pozsarzs/ctt-hw/photos/ctt-ps1.jpg

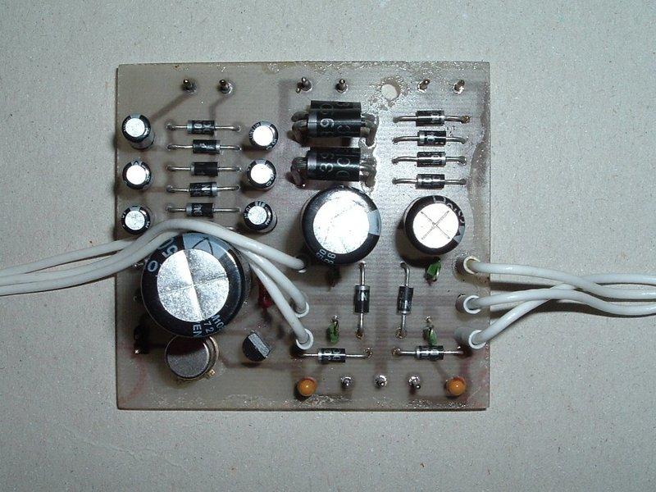
photos/ctt-ps1.jpg
