pozsarzs/ctt-hw/photos/ctt-ps3.jpg

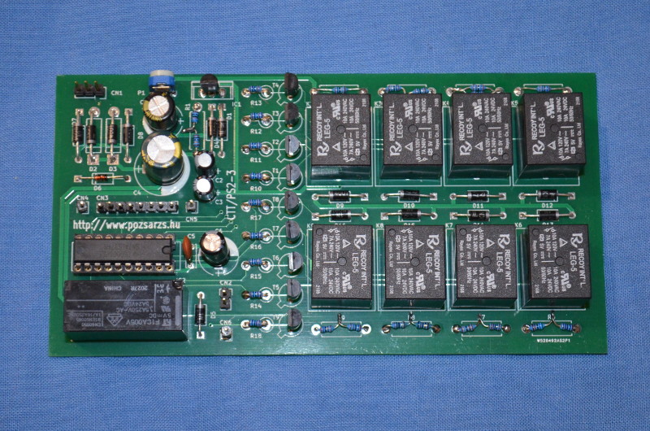
photos/ctt-ps3.jpg
