pozsarzs/ctt-hw/photos/ctt-sw1.jpg

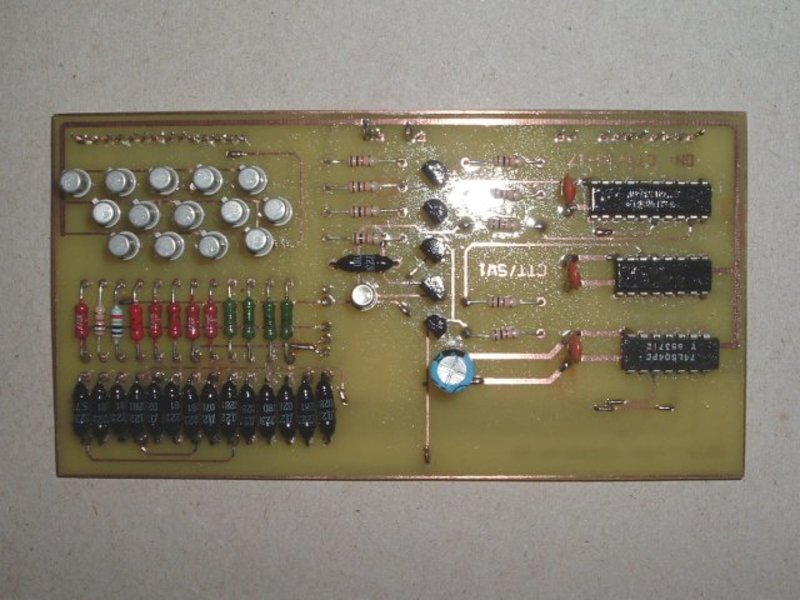
photos/ctt-sw1.jpg
