pozsarzs/ctt-hw/photos/ctt-sw2.jpg

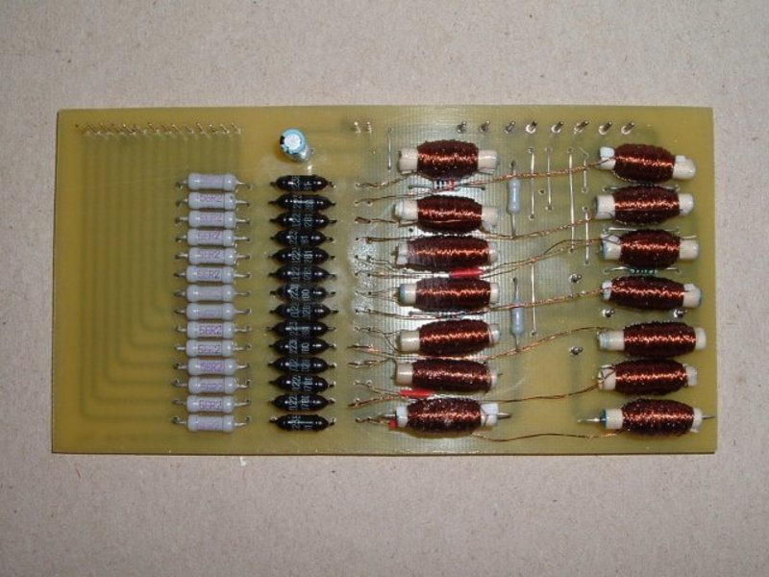
photos/ctt-sw2.jpg
