pozsarzs/ctt-hw/documents/sch_ctt-sw1.pdf

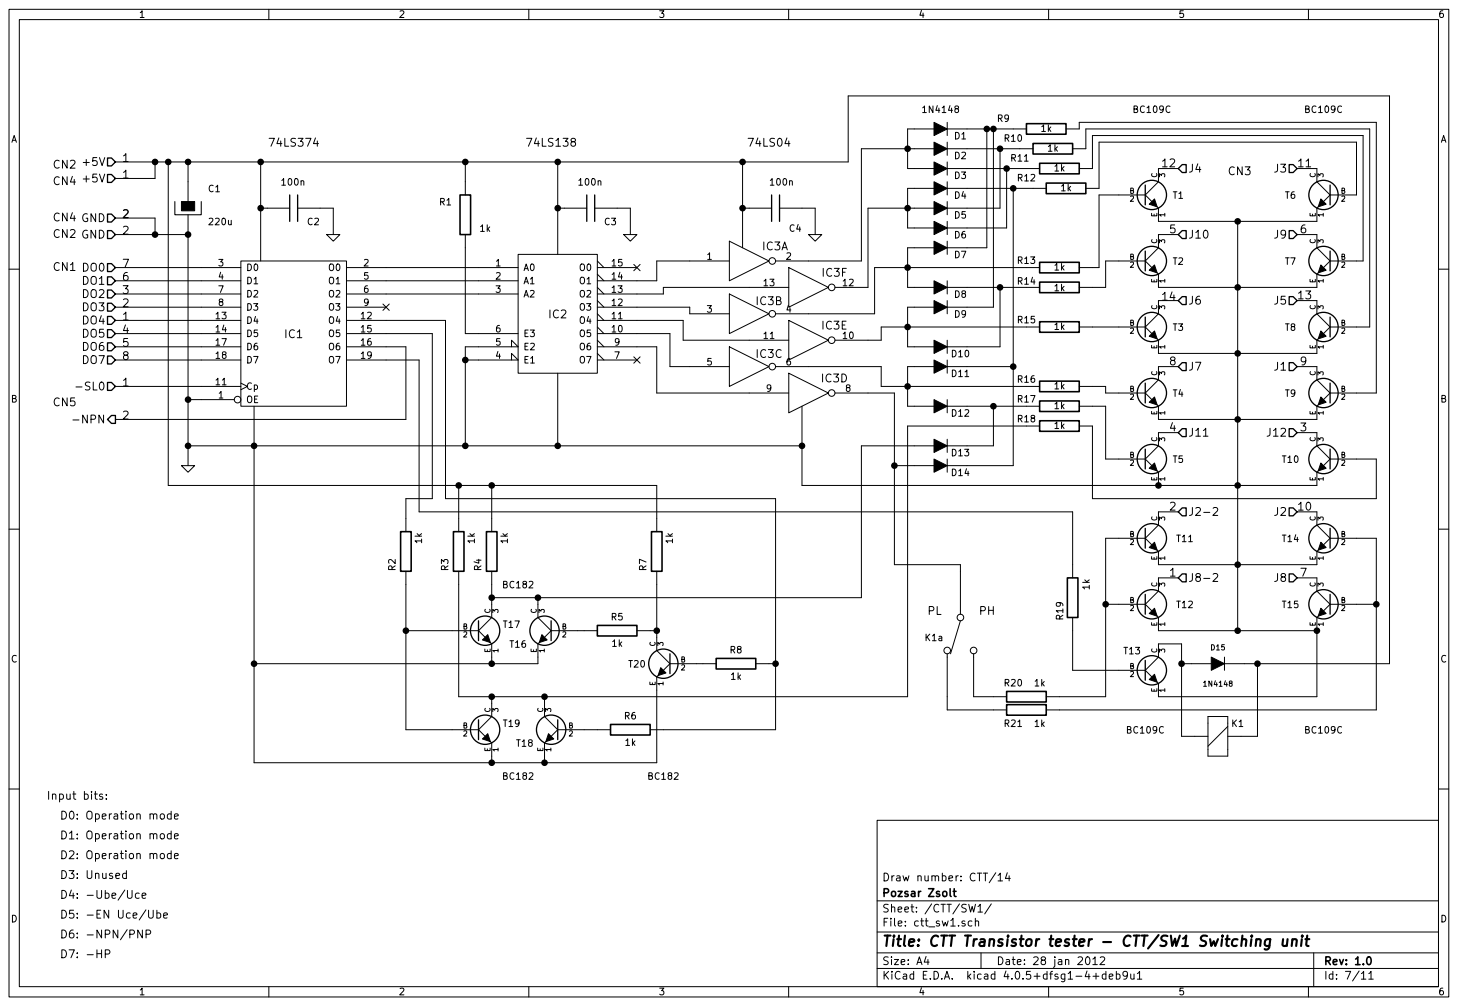
[picture p22: page 1]

D1: Operation mode
D2: Operation mode D3: Unused D4: -Ube/Uce

Id: 7/11 Title: CTT Transistor tester - CTT/SW1 Switching unit
