pozsarzs/ctt-hw/documents/sch_ctt-sw2.pdf

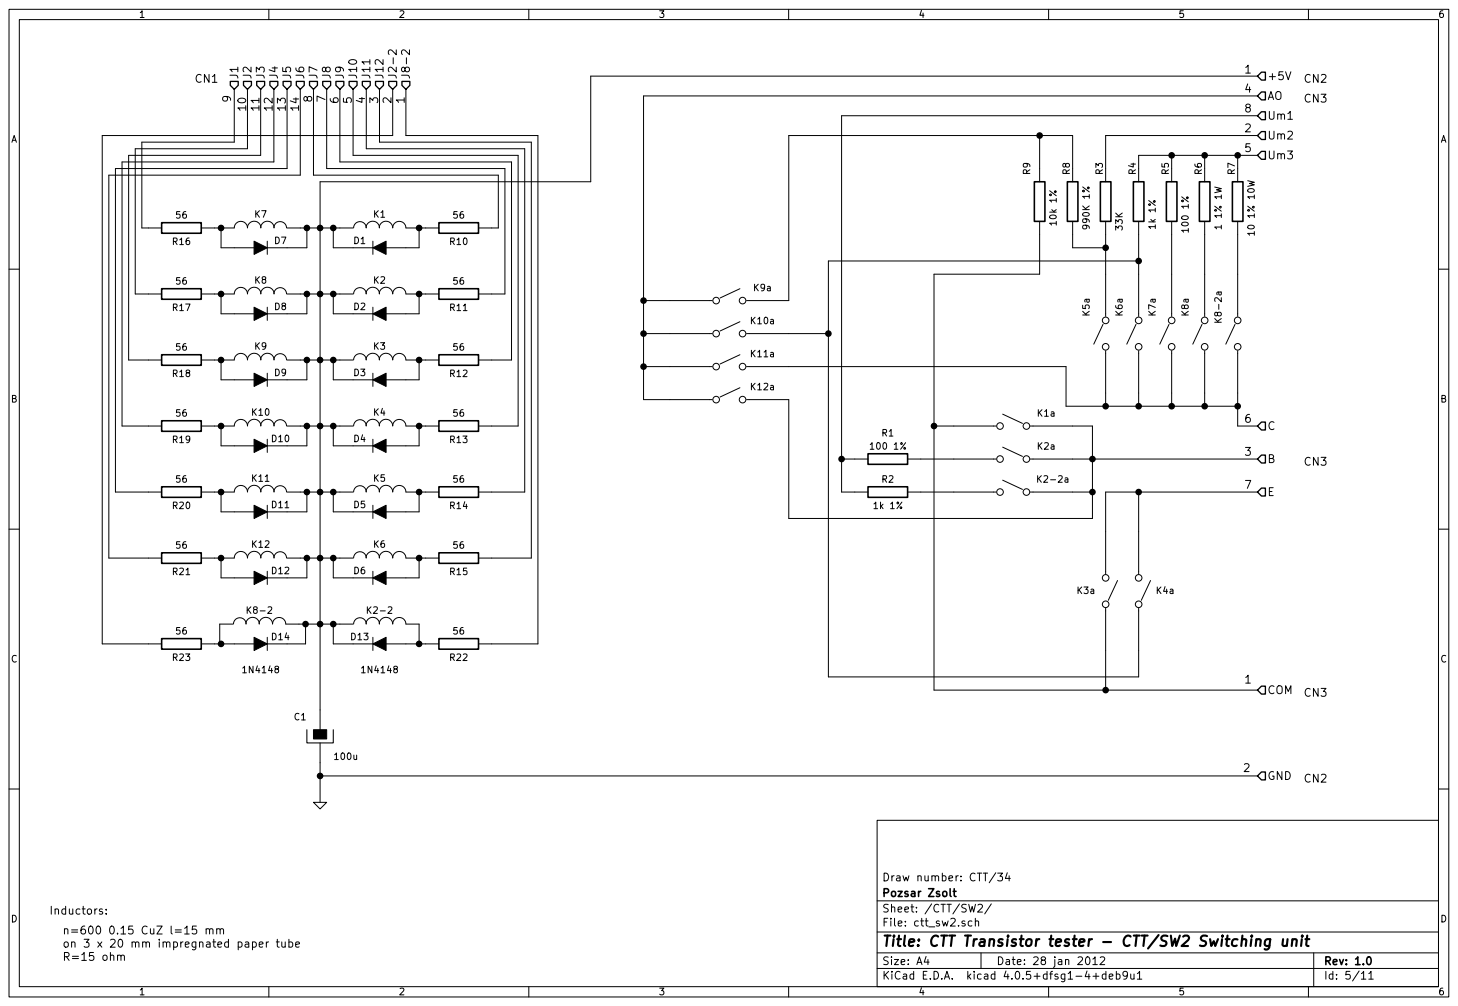
[picture p23: page 1]

File: ctt_sw2.sch Sheet: /CTT/SW2/ Pozsar Zsolt Draw number: CTT/34 on 3 x 20 mm impregnated paper tube R=15 ohm

Id: 5/11 Title: CTT Transistor tester - CTT/SW2 Switching unit
