pozsarzs/ctt-hw/documents/pcb_ctt-sw2-silk.pdf

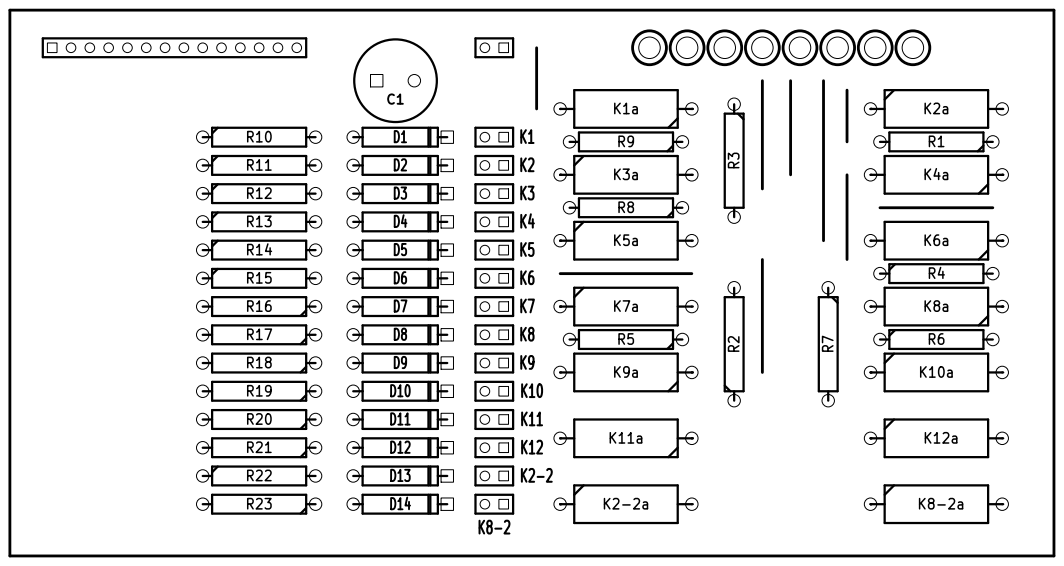
[picture p24: page 1]

File: ctt_sw2.kicad_pcb Sheet: Pozsar Zsolt Draw number: CTT/32-33

Id: 1/1 Title: CTT Transistor tester - CTT/SW2 Switching unit
