pozsarzs/ctt-hw/documents/pcb_ctt-ad-comp.pdf

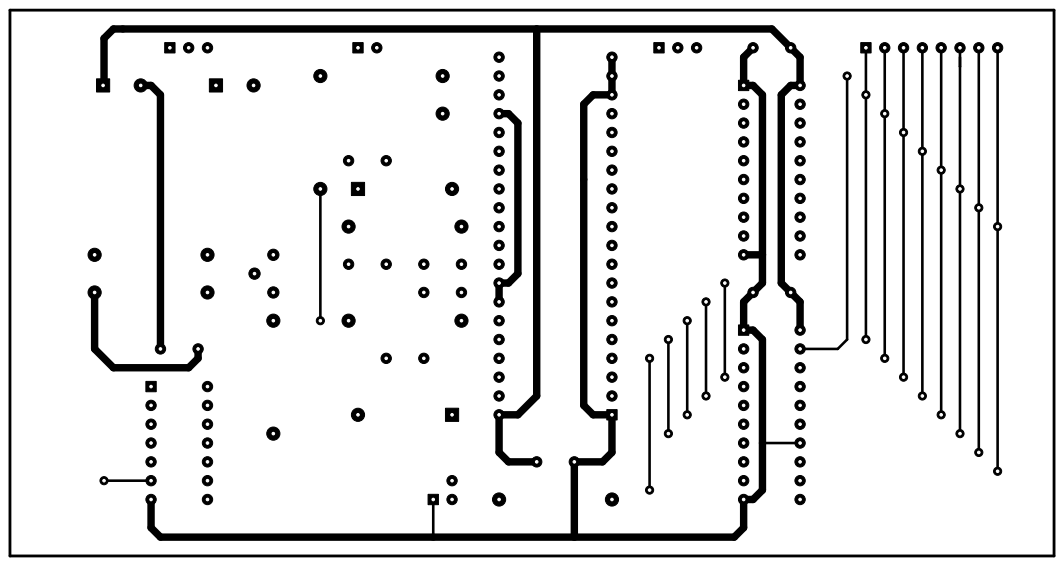
[picture p25: page 1]

File: ctt_ad.kicad_pcb Sheet: Pozsar Zsolt Draw number: CTT/11-13

Id: 1/1 Title: CTT Transistor tester - CTT/AD A/D converter unit
