pozsarzs/ctt-hw/documents/pcb_ctt-dp-comp.pdf

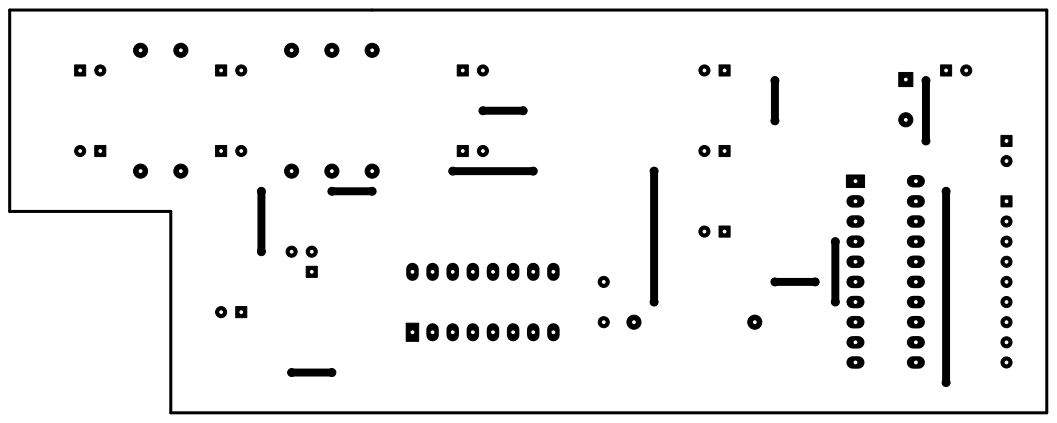
[picture p26: page 1]

File: ctt_dp.kicad_pcb Sheet: Pozsar Zsolt Draw number: CTT/8-9

Id: 1/1 Title: CTT Transistor tester - CTT/DP Display unit
