pozsarzs/ctt-hw/documents/pcb_ctt-if-comp.pdf

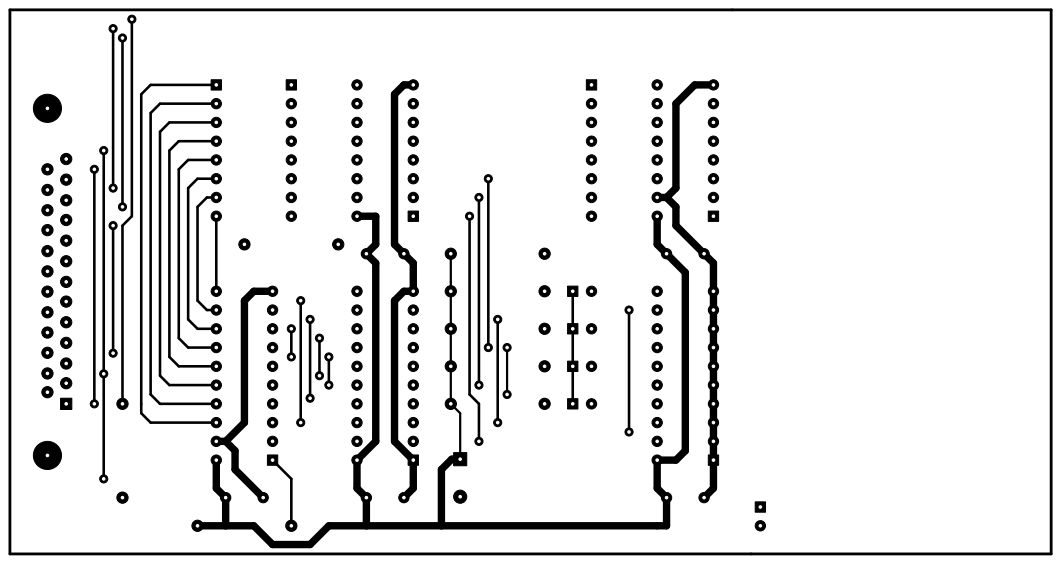
[picture p27: page 1]

File: ctt_if.kicad_pcb Sheet: Pozsar Zsolt Draw number: CTT/4-6

Id: 1/1 Title: CTT Transistor tester - CTT/IF Interface unit
