pozsarzs/ctt-hw/documents/pcb_ctt-ps1-silk.pdf

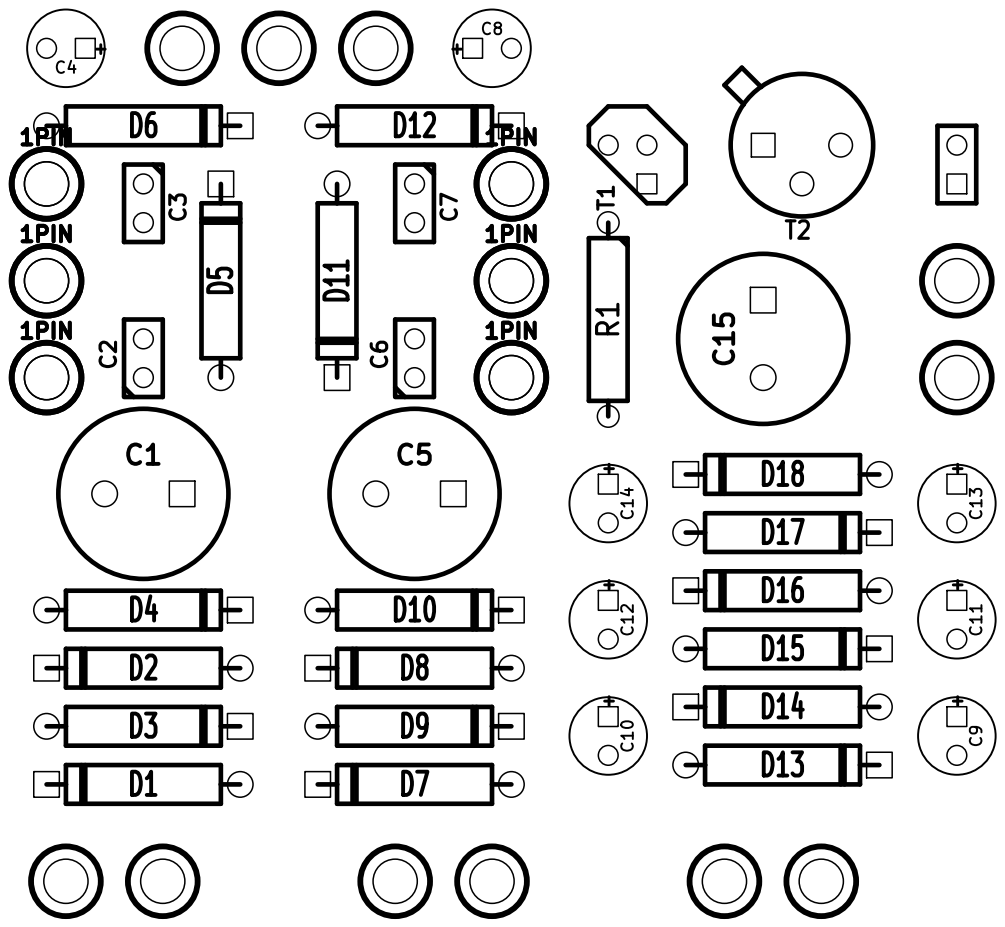
[picture p28: page 1]

File: ctt_ps1.kicad_pcb Sheet: Pozsar Zsolt Draw number: CTT/22-23

Id: 1/1 Title: CTT Transistor tester - CTT/PS1 Power supply unit
