pozsarzs/ctt-hw/documents/pcb_ctt-sc-comp.pdf

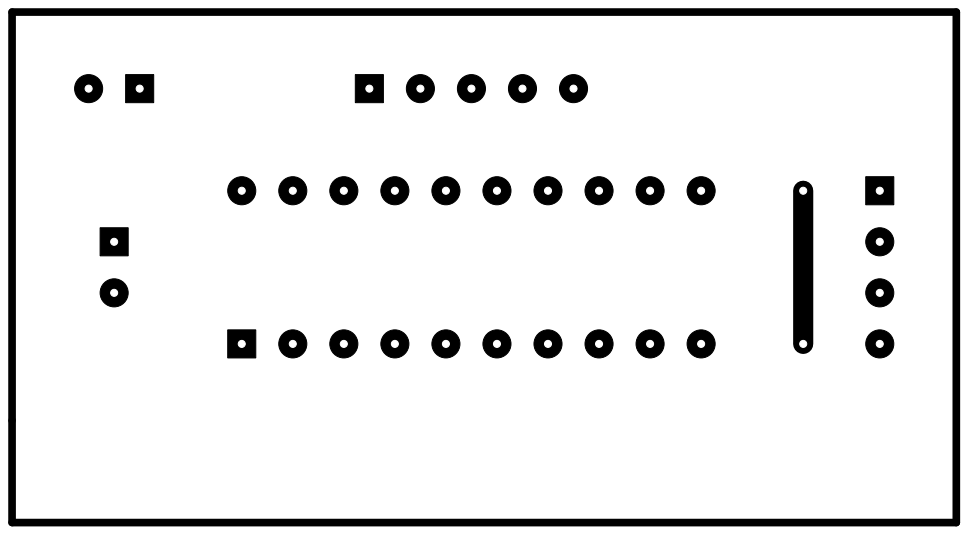
[picture p30: page 1]

File: ctt_sc.kicad_pcb Sheet: Pozsar Zsolt Draw number: CTT/41-42

Id: 1/1 Title: CTT Transistor tester - CTT/SC Status collector unit
