pozsarzs/ctt-hw/documents/pcb_ctt-sc-sold.pdf

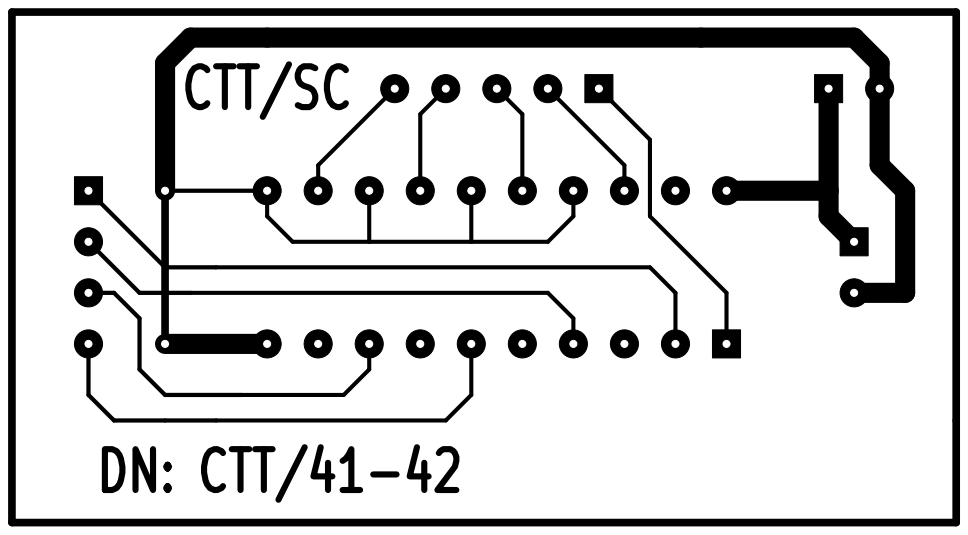
[picture p31: page 1]

File: ctt_sc.kicad_pcb Sheet: Pozsar Zsolt Draw number: CTT/41-42 DN: CTT/41-42

Id: 1/1 Title: CTT Transistor tester - CTT/SC Status collector unit
