pozsarzs/ctt-hw/documents/pcb_ctt-sw1-comp.pdf

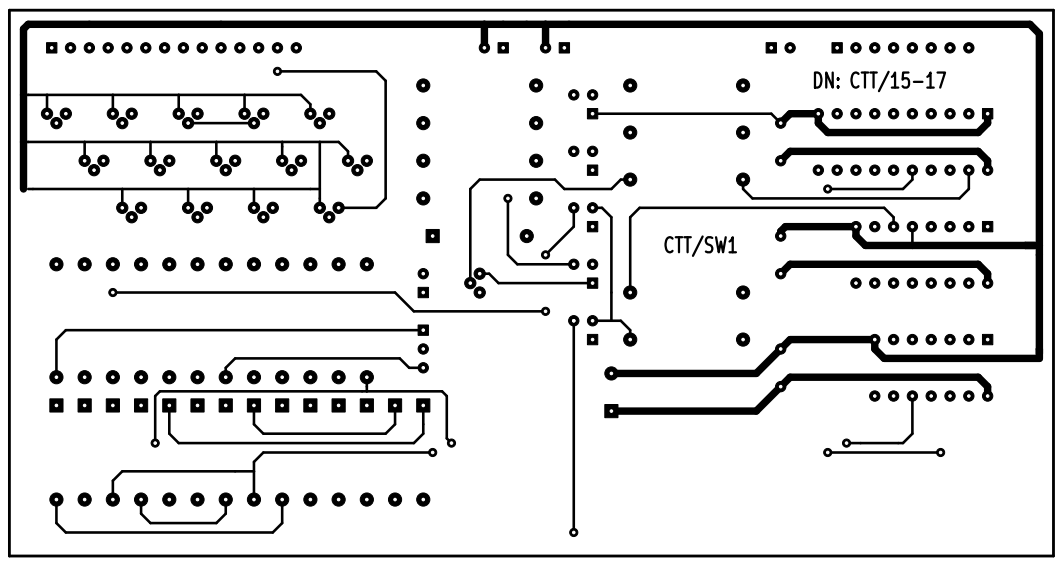
[picture p32: page 1]

File: ctt_sw1.kicad_pcb Sheet: Pozsar Zsolt Draw number: CTT/15-17 CTT/SW1

Id: 1/1 Title: CTT Transistor tester - CTT/SW1 Switching unit
