pozsarzs/ctt-hw/documents/pcb_ctt-sw1-silk.pdf

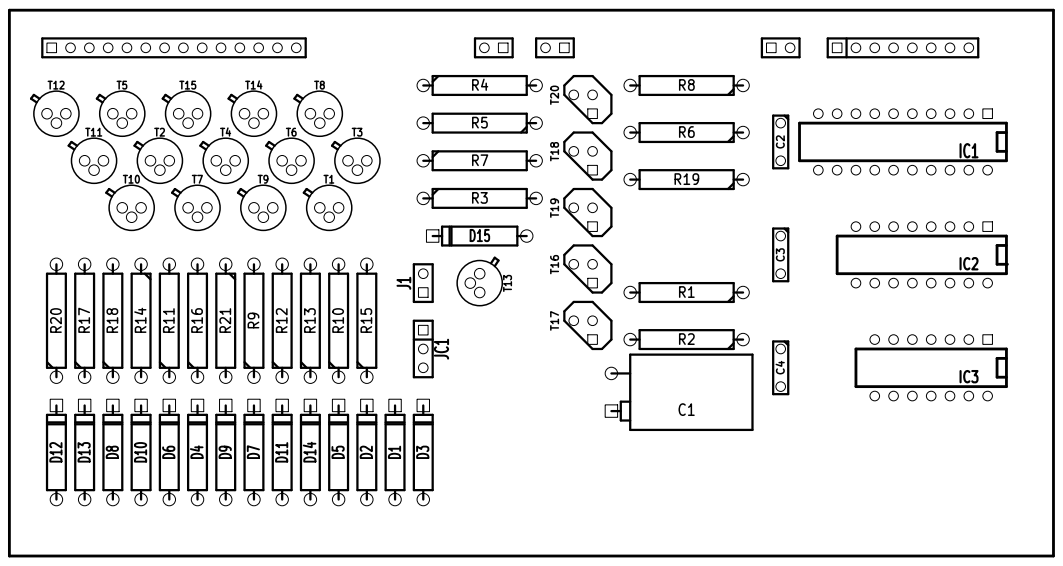
[picture p33: page 1]

File: ctt_sw1.kicad_pcb Sheet: Pozsar Zsolt Draw number: CTT/15-17 C2 C3 C4

Id: 1/1 Title: CTT Transistor tester - CTT/SW1 Switching unit
