pozsarzs/ctt-hw/documents/pcb_ctt-sw1-sold.pdf

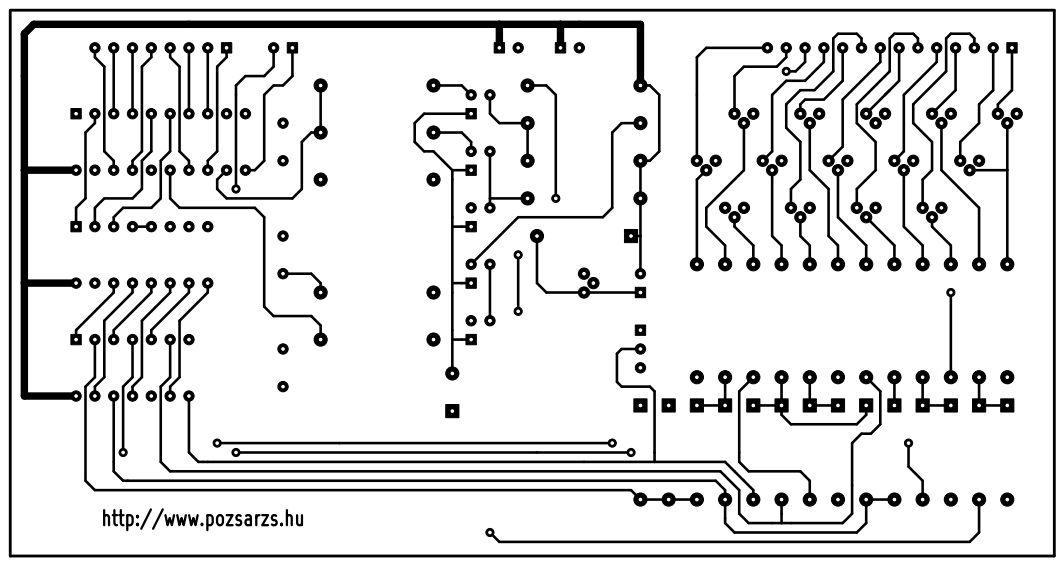
[picture p34: page 1]

File: ctt_sw1.kicad_pcb Sheet: Pozsar Zsolt Draw number: CTT/15-17 http://www.pozsarzs.hu

Id: 1/1 Title: CTT Transistor tester - CTT/SW1 Switching unit
