pozsarzs/ctt-hw/documents/pcb_ctt-sw2-sold.pdf

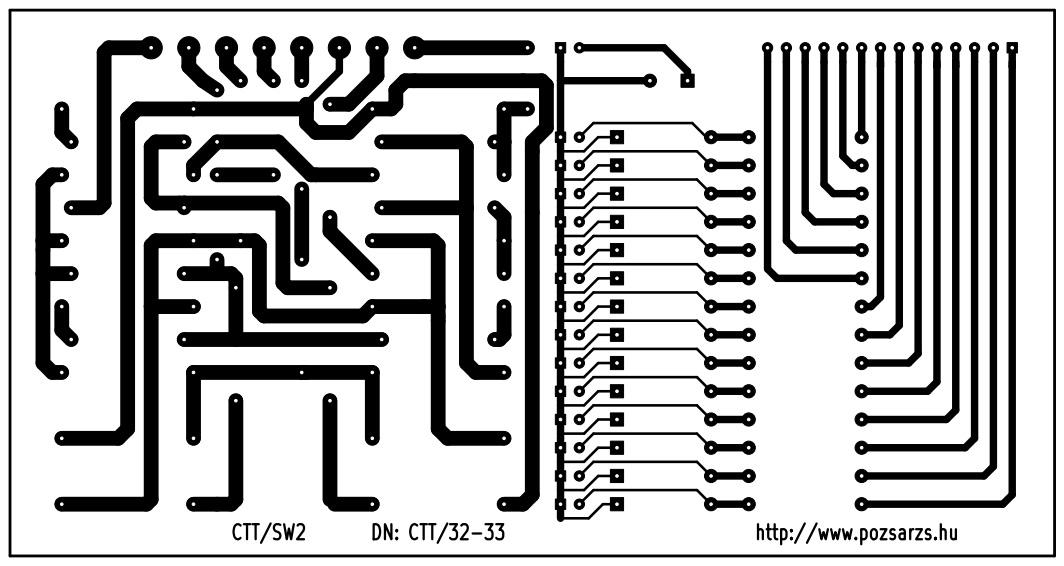
[picture p35: page 1]

Id: 1/1 Title: CTT Transistor tester - CTT/SW2 Switching unit
