pozsarzs/ctt-hw/documents/sch_ctt-ps1.pdf

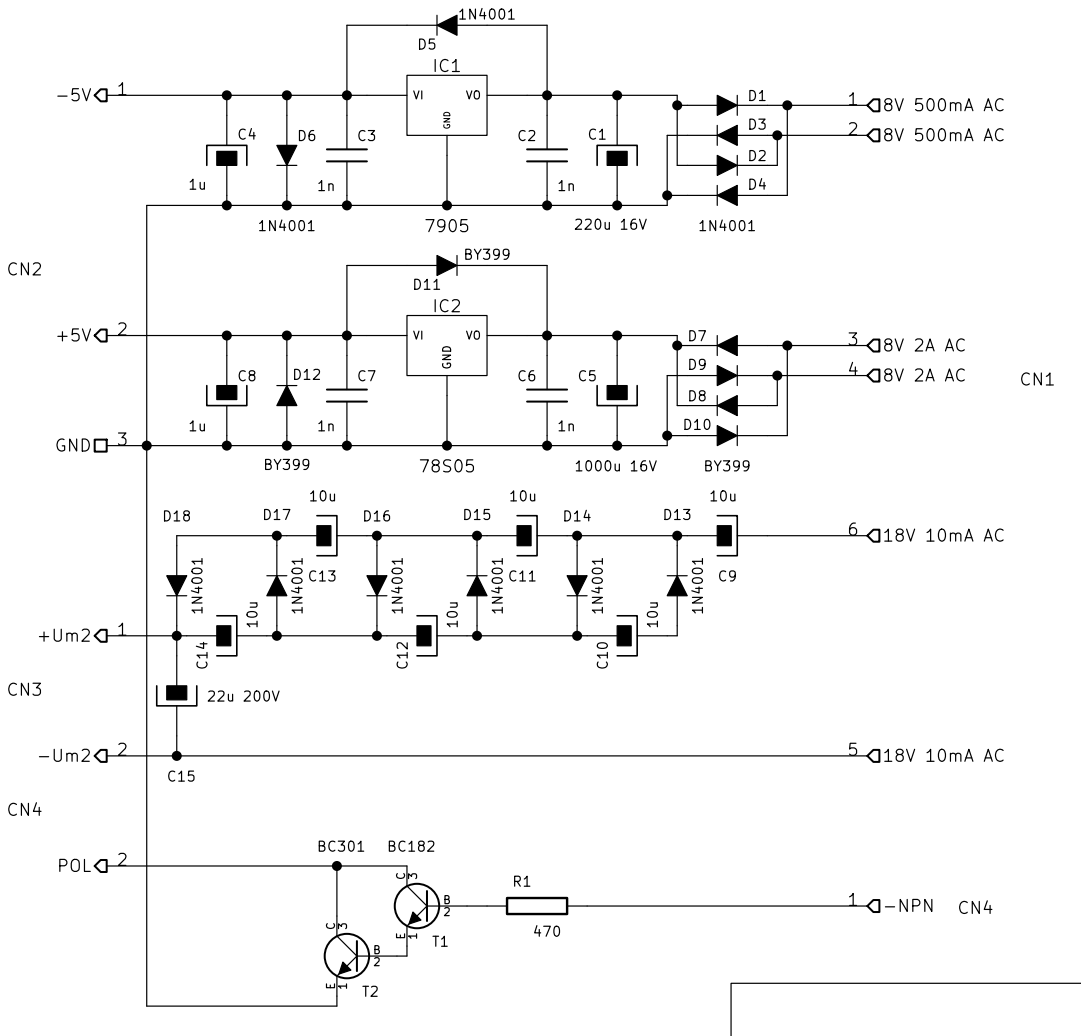
[picture p36: page 1]

File: ctt_ps1.sch Sheet: /CTT/PS1/ Pozsar Zsolt Draw number: CTT/21 6

Id: 11/11 Title: CTT Transistor tester - CTT/PS1 power supply unit
