pozsarzs/ctt-hw/documents/sch_ctt-ad.pdf

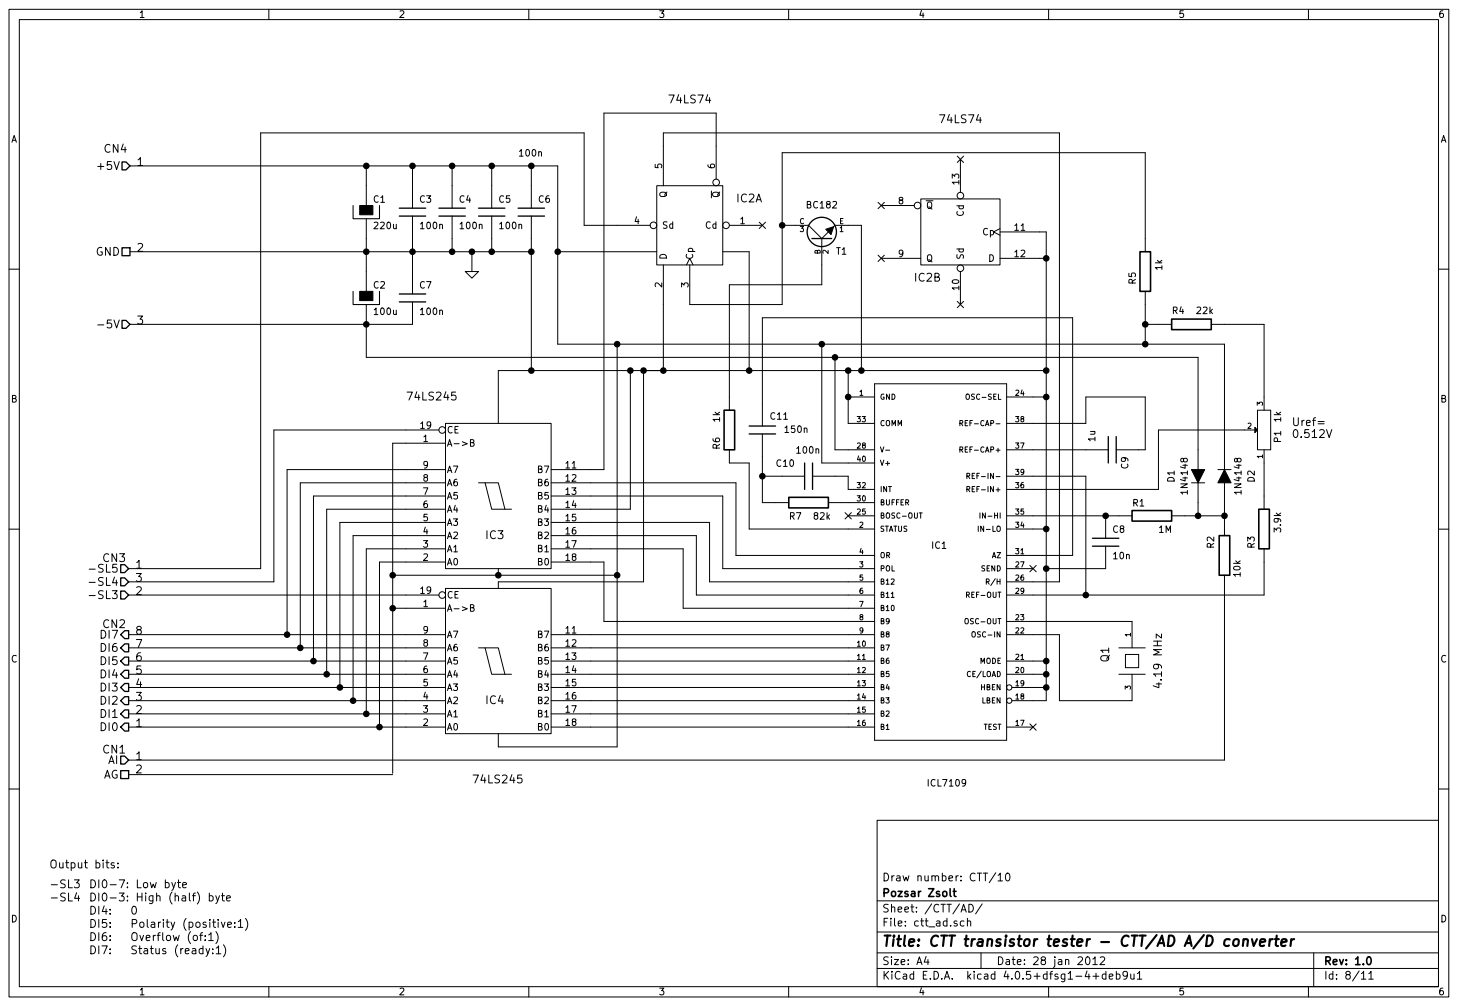
[picture p38: page 1]

File: ctt_ad.sch Sheet: /CTT/AD/ Pozsar Zsolt Draw number: CTT/10 2 AG

DI0-7: Low byte
DI5: Polarity (positive:1) DI4: 0 DI0-3: High (half) byte

Id: 8/11 Title: CTT transistor tester - CTT/AD A/D converter
