pozsarzs/ctt-hw/documents/sch_ctt-dp.pdf

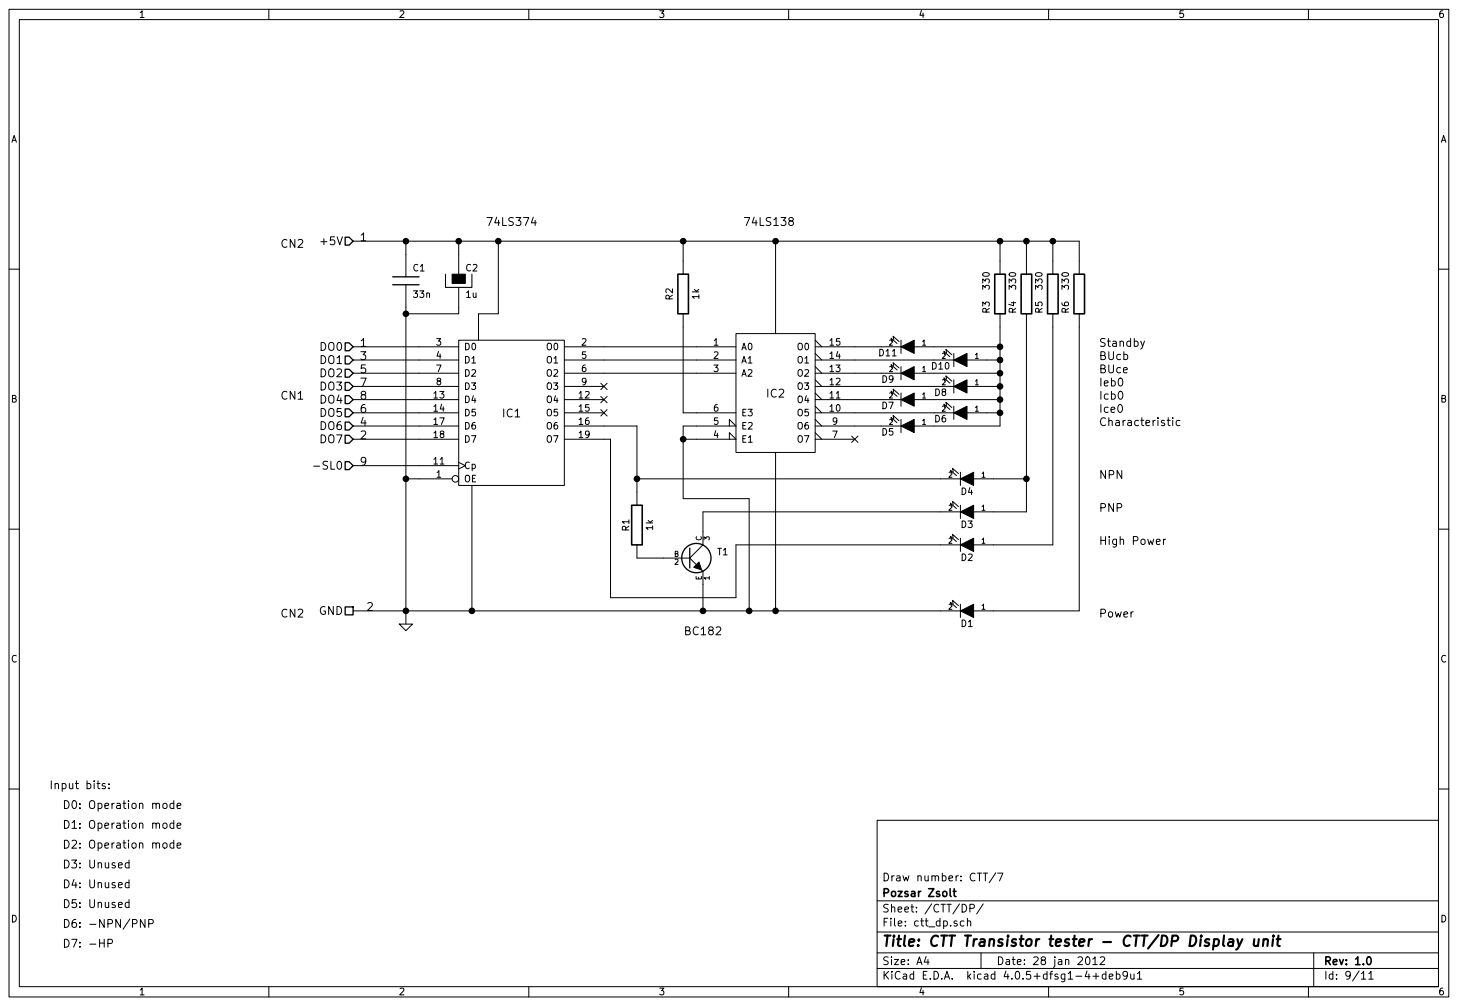
[picture p39: page 1]

1 CN1 D7: -HP D6: -NPN/PNP D5: Unused D4: Unused D3: Unused D2: Operation mode

Ieb0 BUce BUcb Standby NPN

File: ctt_dp.sch Sheet: /CTT/DP/ Pozsar Zsolt Draw number: CTT/7

Id: 9/11 Title: CTT Transistor tester - CTT/DP Display unit
