pozsarzs/ctt-hw/documents/sch_ctt-if.pdf

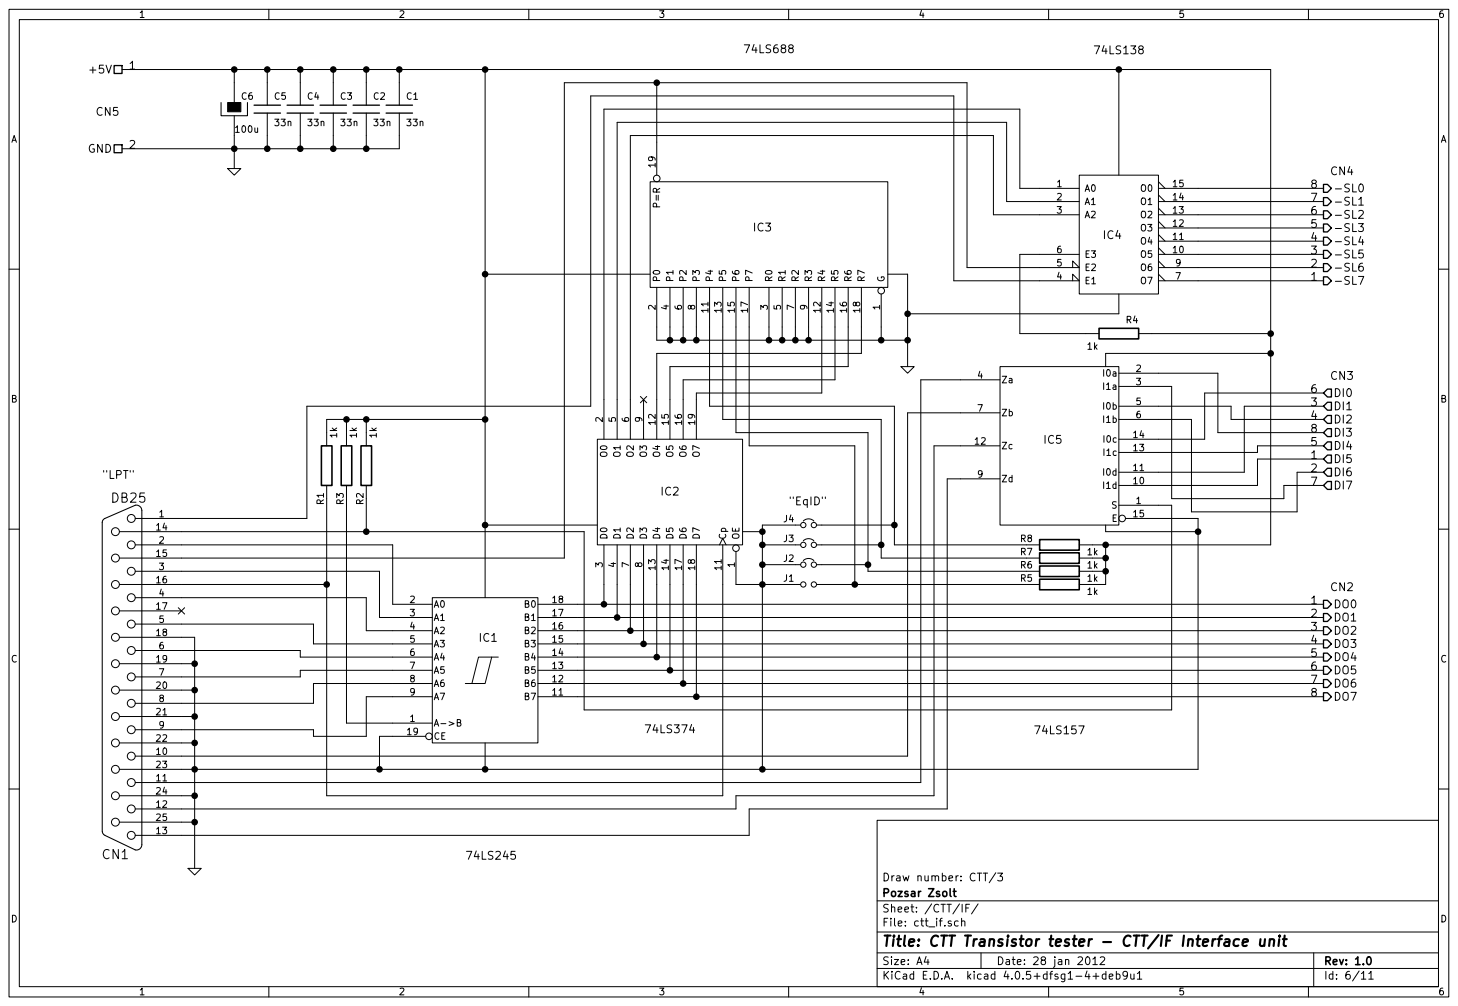
[picture p40: page 1]

23
11
24

Id: 6/11 Title: CTT Transistor tester - CTT/IF Interface unit
