pozsarzs/ctt-hw/documents/pcb_ctt-ad-sold.pdf

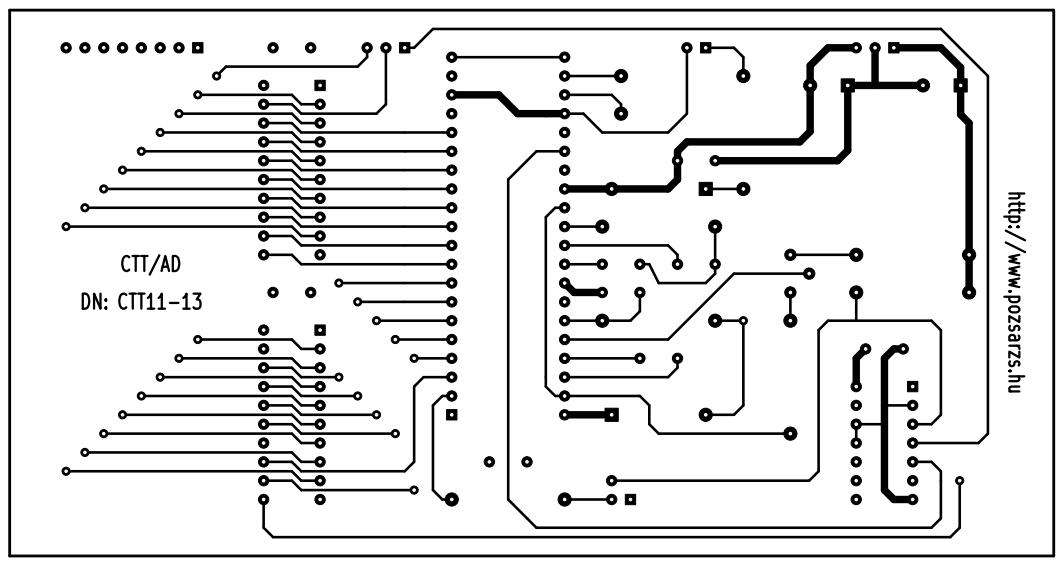
[picture p41: page 1]

Id: 1/1 Title: CTT Transistor tester - CTT/AD A/D converter unit
