pozsarzs/ctt-hw/documents/pcb_ctt-dp-sold.pdf

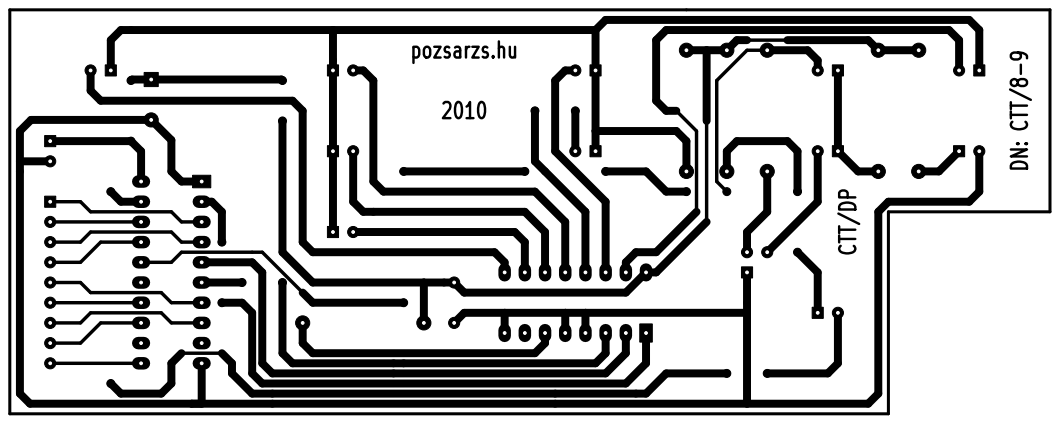
[picture p42: page 1]

Id: 1/1 Title: CTT Transistor tester - CTT/DP Display unit
