pozsarzs/ctt-hw/documents/pcb_ctt-if-silk.pdf

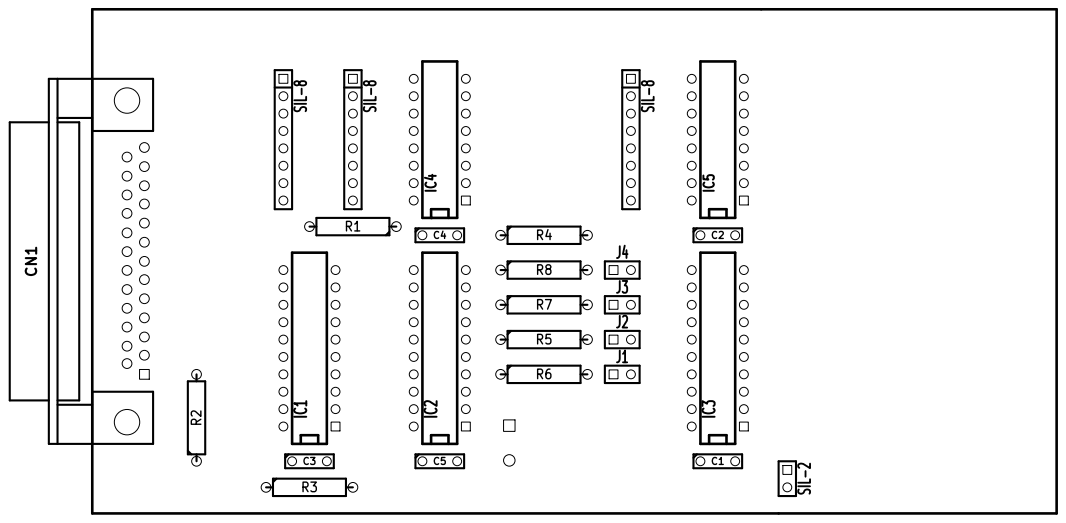
[picture p43: page 1]

Id: 1/1 Title: CTT Transistor tester - CTT/IF Interface unit
