pozsarzs/ctt-hw/documents/pcb_ctt-if-sold.pdf

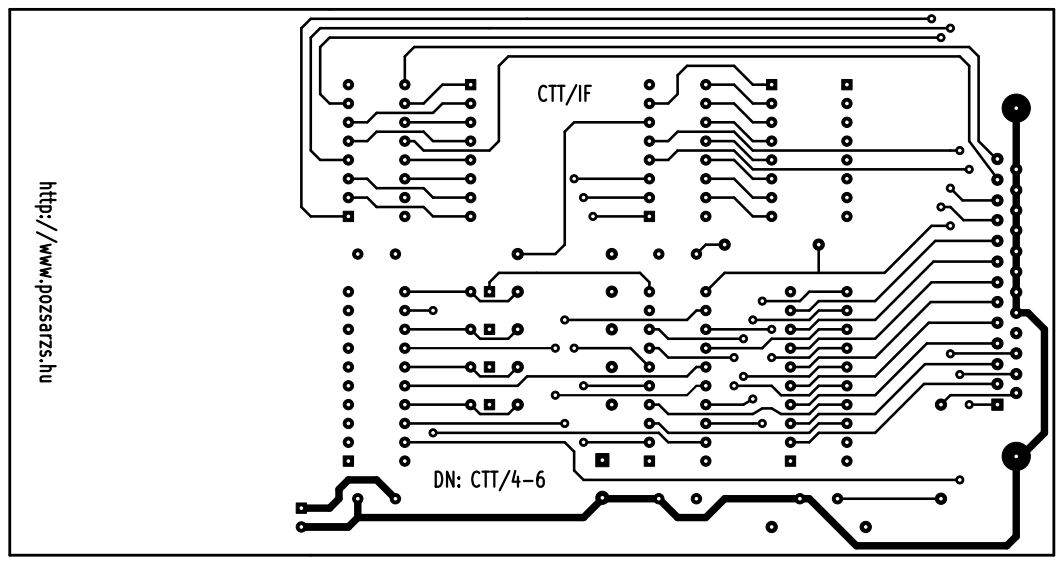
[picture p44: page 1]

Id: 1/1 Title: CTT Transistor tester - CTT/IF Interface unit
