pozsarzs/ctt-hw/documents/pcb_ctt-sc-silk.pdf

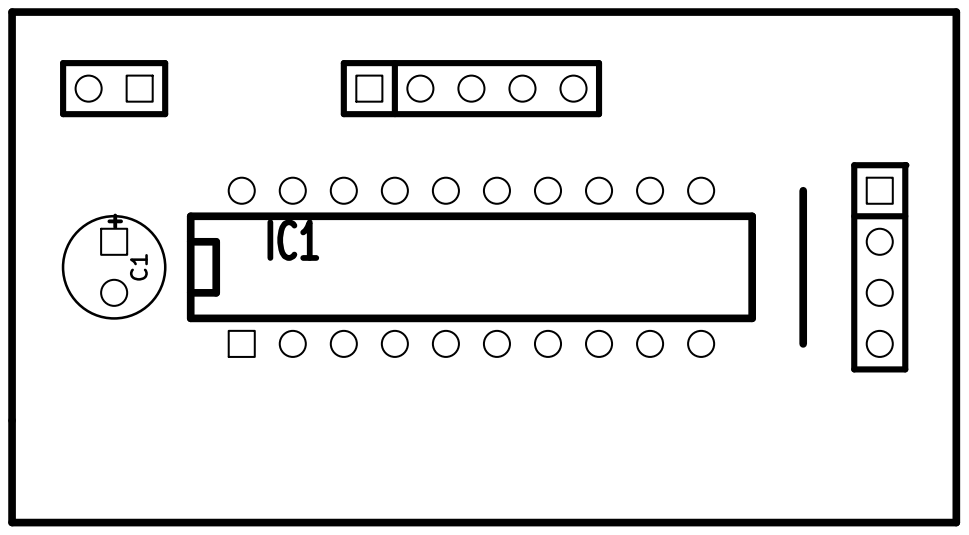
[picture p45: page 1]

Id: 1/1 Title: CTT Transistor tester - CTT/SC Status collector unit
