pozsarzs/ctt-hw/documents/sch_ctt-sc.pdf

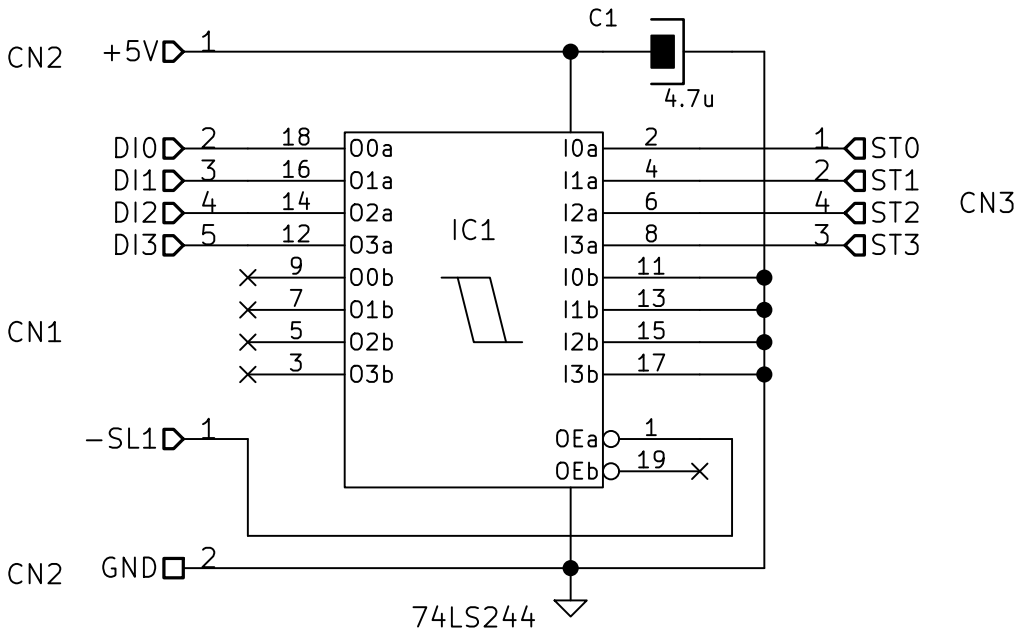
[picture p46: page 1]

File: ctt_sc.sch Sheet: /CTT/SC/ Pozsar Zsolt Draw number: CTT/40

Id: 3/11 Title: CTT Transistor tester - CTT/SC Status collector unit
