pozsarzs/ctt-hw/ctt_ad/ctt_ad.sch

## KiCad design ctt_ad/ctt_ad.sch (2012-01-08)

Schematic: ctt_ad.sch

Parts:
C1: 220u
C2: 100u
C3, C4, C5, C6, C7, C10: 100n
C8: 10n
C9: 1u
C11: 150n
D1, D2: 1N4148
IC1: ICL7109; maxim-DIL40
IC2: 74LS74
IC3, IC4: 74LS245
P1: 1k
Q1: 4.19 MHz
R1: 1M
R2: 10k
R3: 3.9k
R4: 22k
R5, R6: 1k
R7: 82k
T1: BC182

Notes on the sheet:
Uref=0.512V
-SL4
-SL3
CN4
CN3
CN2
CN1
DI7: Status (ready:1)
DI6: Overflow (of:1)
DI5: Polarity (positive:1)
DB4: 0
DI0-3: High (half) byte
DI0-7: Low byte
