pozsarzs/ctt-hw/ctt_dp/ctt_dp.sch

## KiCad design ctt_dp/ctt_dp.sch (2012-01-08)

Schematic: ctt_dp.sch

Parts:
C1: 33n
C2: 1u
D1, D2, D3, D4, D5, D6, D7, D8, D9, D10, D11: LED
IC1: 74LS374
IC2: 74LS138
R1, R2: 1k
R3, R4, R5, R6: 330
T1: BC182

Notes on the sheet:
CN2
CN1
D7: -HP
D6: -NPN/PNP
D5: Unused
D4: Unused
D3: Unused
D2: Operation mode
D1: Operation mode
D0: Operation mode
Input bits:
Characteristic
Ice0
Icb0
Ieb0
BUce
BUcb
Standby
NPN
PNP
High Power
Power
