pozsarzs/ctt-hw/ctt_if/ctt_if.sch

## KiCad design ctt_if/ctt_if.sch (2012-01-08)

Schematic: ctt_if.sch

Parts:
C1, C2, C3, C4, C5: 33n
C6: 100u
CN1: DB25
IC1: 74LS245
IC2: 74LS374
IC3: 74LS688
IC4: 74LS138
IC5: 74LS157
J1, J2, J3, J4: JUMPER
R1, R2, R3, R4, R5, R6, R7, R8: 1k

Notes on the sheet:
J2-4: Close
J1: Open
"Eq ID"
CN2
CN3
CN4
CN5
"LPT"
