pozsarzs/ctt-hw/ctt_ps/ctt_ps1.sch

## KiCad design ctt_ps/ctt_ps1.sch (2012-01-08)

Schematic: ctt_ps1.sch

Parts:
C1: 220u 16V
C2, C3, C6, C7: 1n
C4, C8: 1u
C5: 1000u 16V
C9, C10, C11, C12, C13, C14: 10u
C15: 22u 200V
D1, D2, D3, D4, D5, D6, D8, D9, D10, D13, D14, D15, D16, D17, D18: 1N4001
D7, D11, D12: BY399
IC1: 7905
IC2: 78S05
R1: 470
T1: BC182
T2: BC301

Notes on the sheet:
CN4
CN3
CN2
CN1
