pozsarzs/ctt-hw/ctt_ps/ctt_ps3.sch

## KiCad design ctt_ps/ctt_ps3.sch (2012-01-19)

Schematic: ctt_ps3.sch

Parts:
C1, C2: 2200u 16V
C3: 10u 6V
C4, C5: 33n
C6: 10u
D1, D2, D3, D4: BY399
D5: 1,2V
IC1: DAC0832
IC2: LF351
IC3, IC4, IC5, IC6, IC7, IC8, IC9, IC10: OPTONPN
IC11: 74LS374
J1: RELAY
JC1, JC2: SWITCH_INV
P1: 100k
R1: 300
R2: 12
R3, R4: 1,5K
R5: 4,3k
R6, R7, R16, R17, R18, R19, R20, R21, R22, R23: 1k
R8, R9, R10, R11, R12, R13, R14, R15: 4,7k
R24: 470
T1, T2, T3: BC212
T4: BC109
T5: BC182

Notes on the sheet:
ISOLATED PART
"set zero"
