pozsarzs/ctt-hw/ctt_ps/ctt_ps4.sch

## KiCad design ctt_ps/ctt_ps4.sch (2012-01-08)

Schematic: ctt_ps4.sch

Parts:
F1: 500 mA T
P: INDUCTOR
S1, S2, S3, S4, S5, S6, S7: INDUCTOR
SW1a, SW1b: SPST

Notes on the sheet:
CN2
CN1
Tr1
