pozsarzs/ctt-hw/ctt_sc/ctt_sc.sch

## KiCad design ctt_sc/ctt_sc.sch (2012-01-08)

Schematic: ctt_sc.sch

Parts:
C1: 4.7u
IC1: 74LS244

Notes on the sheet:
CN2
CN1
CN3
