pozsarzs/ctt-hw/ctt_sw/ctt_sw1.sch

## KiCad design ctt_sw/ctt_sw1.sch (2012-01-08)

Schematic: ctt_sw1.sch

Parts:
C1: 220u
C2, C3, C4: 100n
D1, D2, D3, D4, D5, D6, D7, D8, D9, D10, D11, D12, D13, D14, D15: 1N4148
IC1: 74LS374
IC2: 74LS138
IC3: 74LS04
J1: RELAY
JC1: SWITCH_INV
R1, R2, R3, R4, R5, R6, R7, R8, R9, R10, R11, R12, R13, R14, R15, R16, R17, R18, R19, R20, R21: 1k
T1, T2, T3, T4, T5, T6, T7, T8, T9, T10, T11, T12, T13, T14, T15: BC109C
T16, T17, T18, T19, T20: BC182

Notes on the sheet:
CN5
CN3
CN4
CN2
D0: Operation mode
D1: Operation mode
D2: Operation mode
D3: Unused
D4: -Ube/Uce
D5: -EN Uce/Ube
D6: -NPN/PNP
D7: -HP
Input bits
CN1
