pozsarzs/ctt-hw/ctt_sw/ctt_sw2.sch

## KiCad design ctt_sw/ctt_sw2.sch (2012-01-08)

Schematic: ctt_sw2.sch

Parts:
C1: 100u
D1, D2, D3, D4, D5, D6, D7, D8, D9, D10, D11, D12, D13, D14: 1N4148
J1, J2, J2-2, J3, J4, J5, J6, J7, J8, J8-2, J9, J10, J11, J12: Reed relay
JC1, JC2, JC2-2, JC3, JC4, JC5, JC6, JC7, JC8, JC8-2, JC9, JC10, JC11, JC12: SPST
R1, R5: 100 1%
R2, R4: 1k 1%
R3: 33K
R6: 1 1% 1W
R7: 10 1% 10W
R8: 990K 1%
R9: 10k 1%
R10, R11, R12, R13, R14, R15, R16, R17, R18, R19, R20, R21, R22, R23: 56

Notes on the sheet:
on 3 x 20 mm impregnated paper tube
R=15 ohm
n=600 0.15 CuZ l=15 mm
Inductors:
CN3
CN2
CN1
